phpbbireland/echo/ayla/kle/ansi_2024-11-16.png

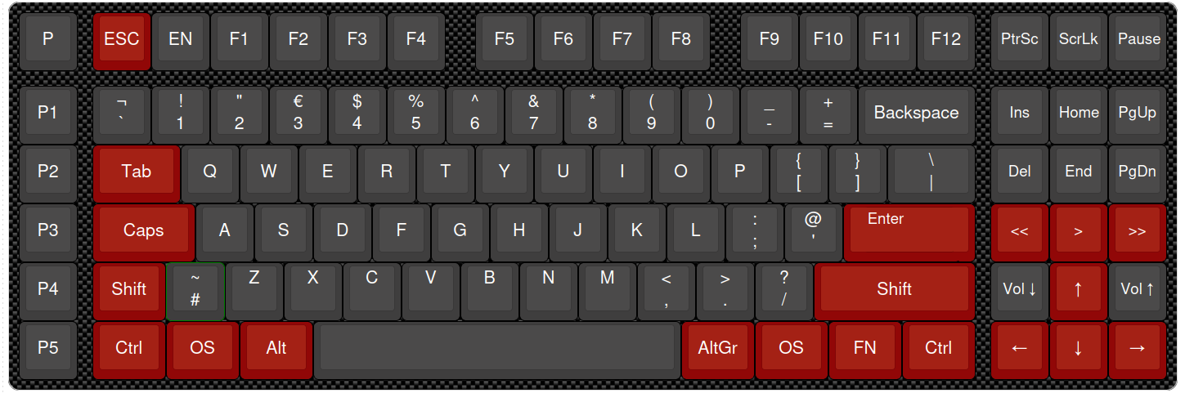
ayla/kle/ansi_2024-11-16.png
