phpbbireland/echo/ayla/kle/ayla80-16-11-24.png

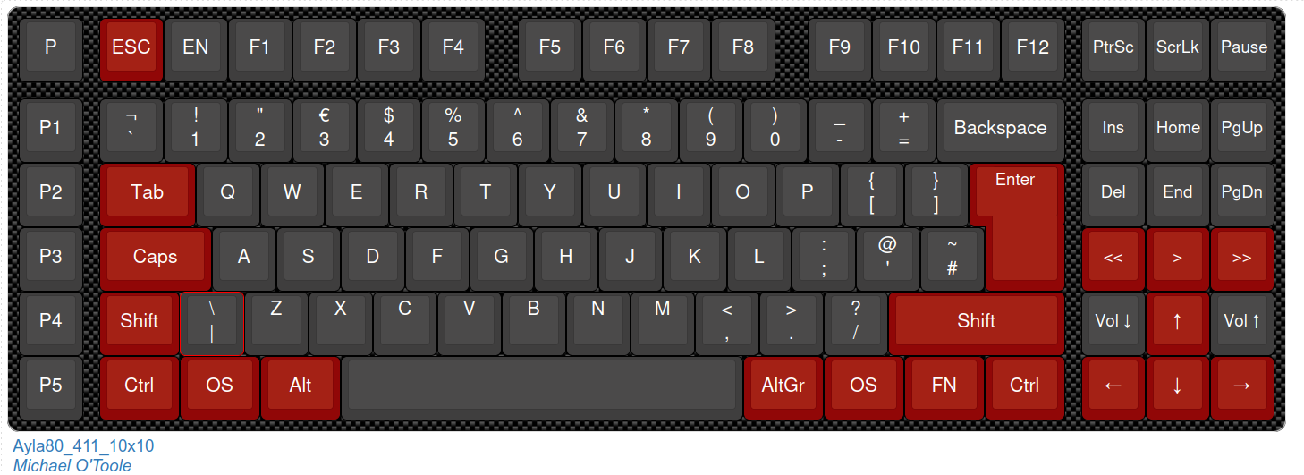
ayla/kle/ayla80-16-11-24.png
