phpbbireland/echo/ayla/kle/kle_ansi.png

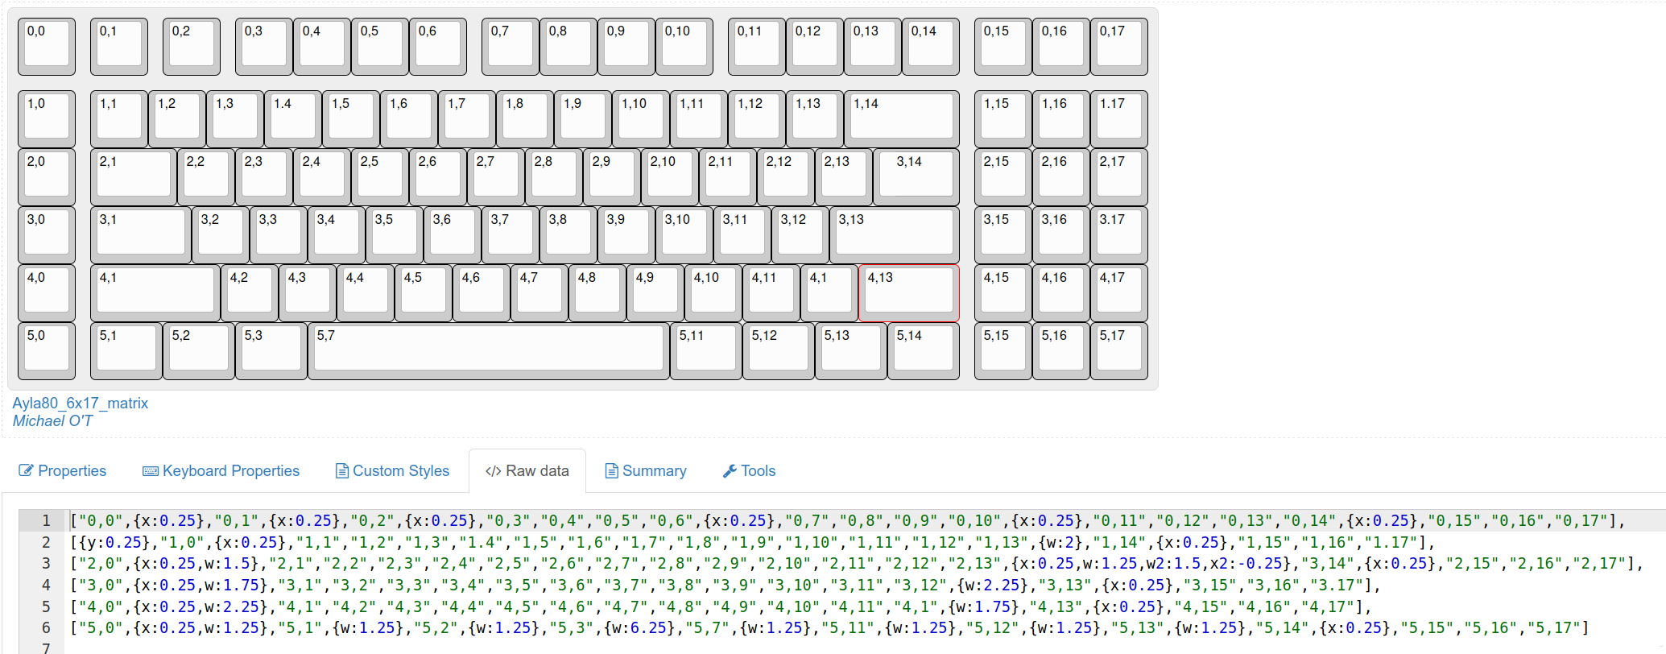
ayla/kle/kle_ansi.png
