phpbbireland/echo/E014/images/kle_en014_keyboard_layout.png

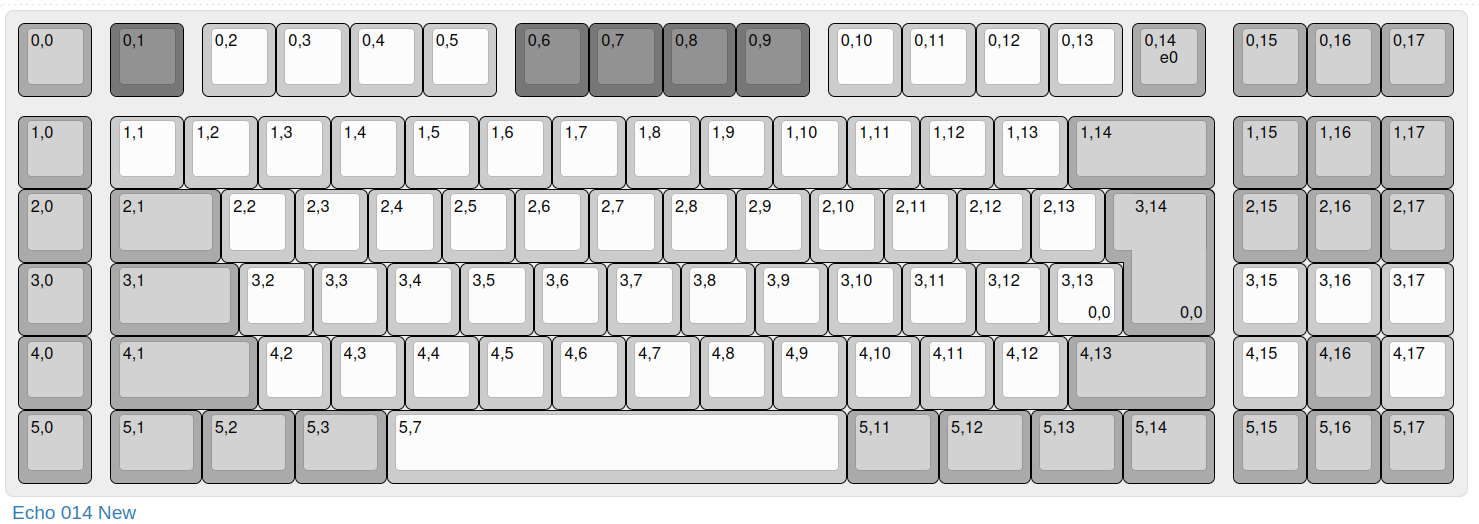
E014/images/kle_en014_keyboard_layout.png
