phpbbireland/echo/iso_encoder/store/kle/kle.png

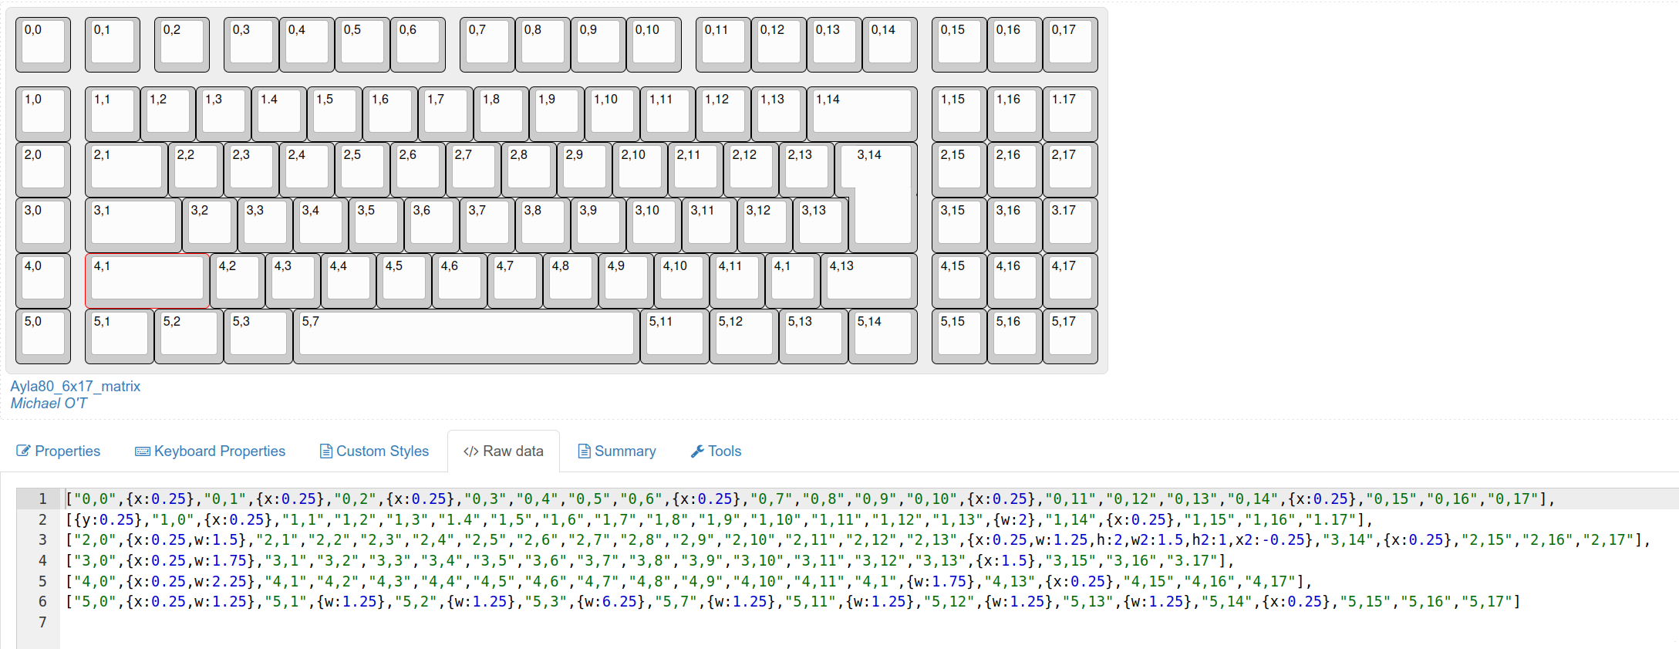
iso_encoder/store/kle/kle.png
