phpbbireland/echo/iso_encoder/store/usevia/usevia-image-ansi.png

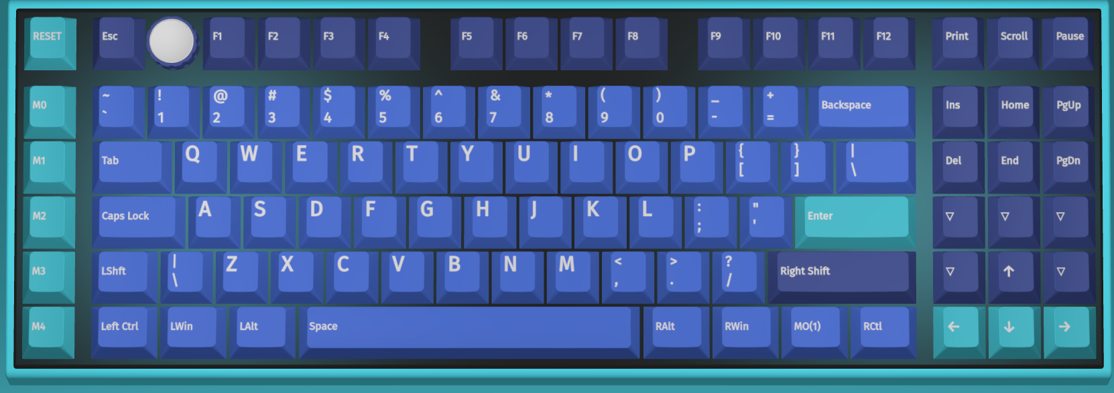
iso_encoder/store/usevia/usevia-image-ansi.png
