phpbbireland/echo/iso_encoder/store/usevia/usevia_image1.png

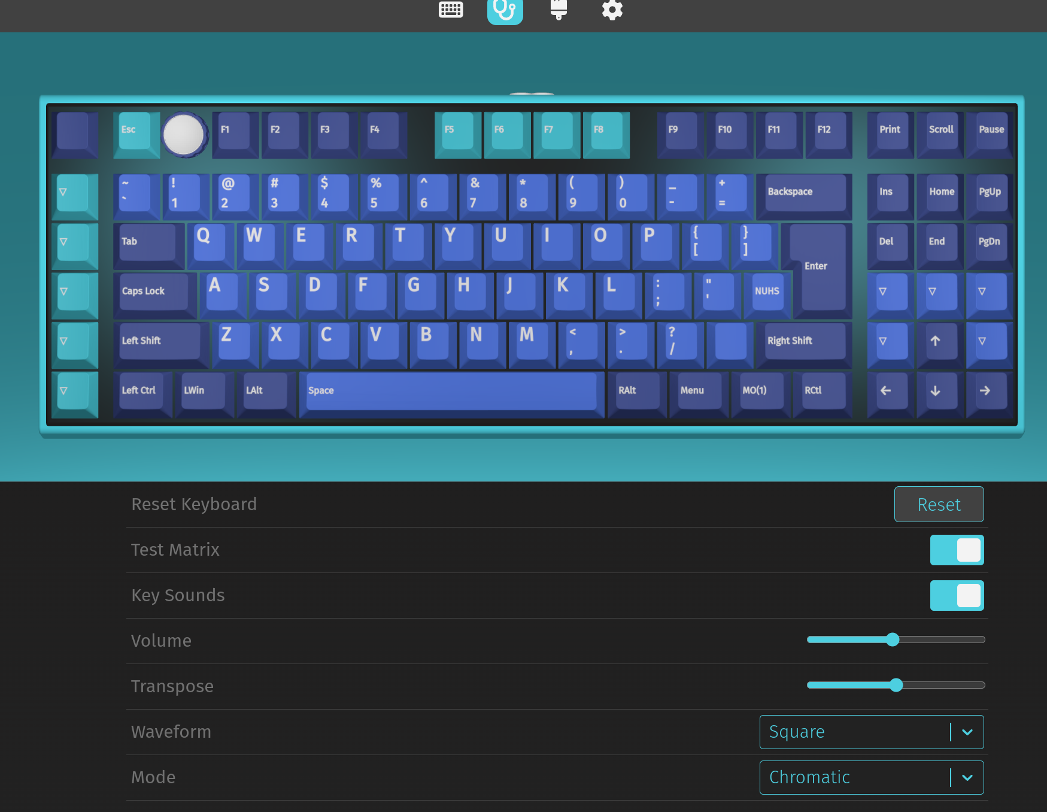
iso_encoder/store/usevia/usevia_image1.png
