phpbbireland/echo/iso_encoder_rp2040_er2/images/kle_image2.png

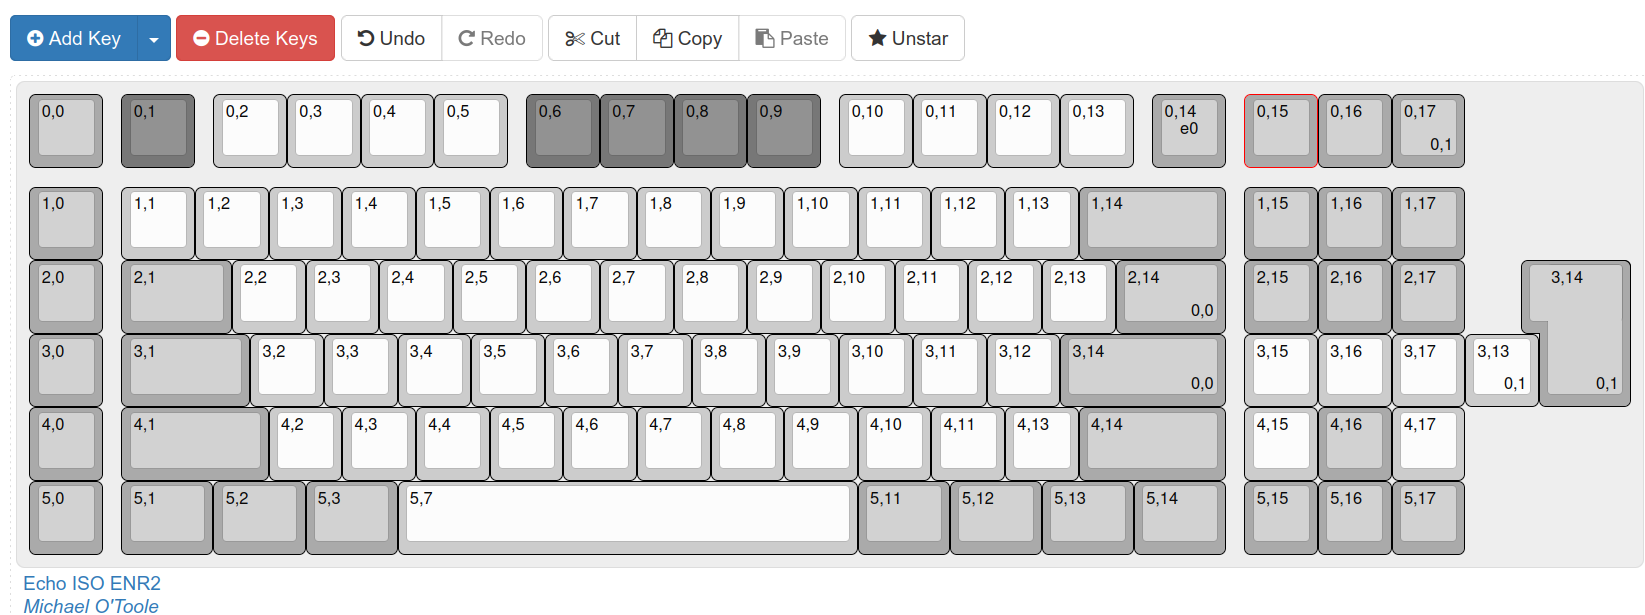
iso_encoder_rp2040_er2/images/kle_image2.png
