phpbbireland/echo/iso_encoder_rp2040_er2/images/usevia.app_image.png

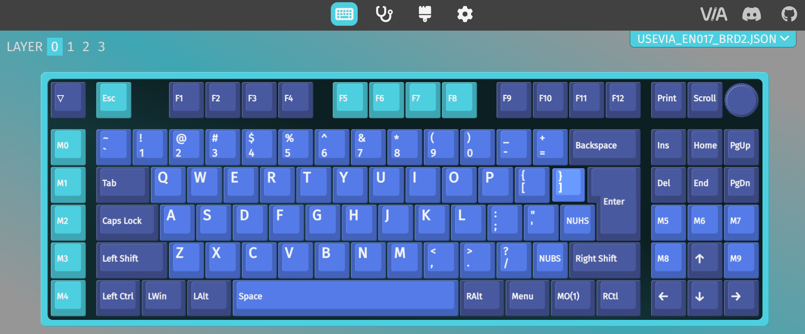
iso_encoder_rp2040_er2/images/usevia.app_image.png
