phpbbireland/echo/Module34C/Module34C.png

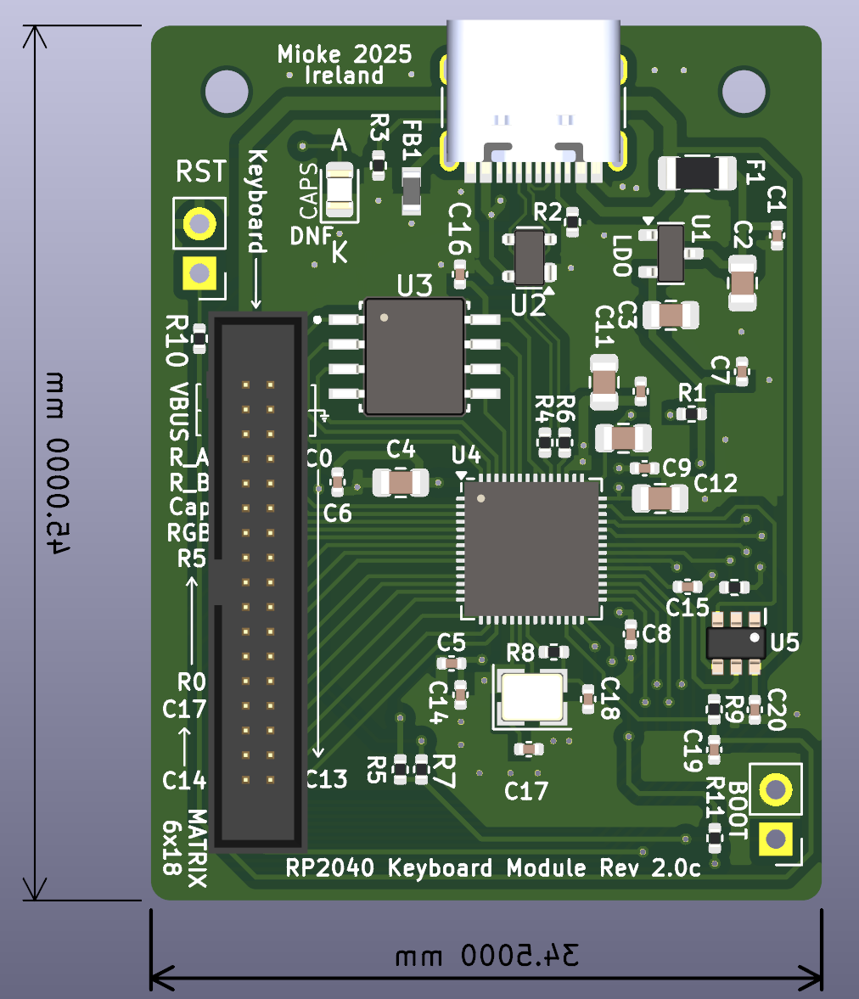
Module34C/Module34C.png
