phpbbireland/echo/RP2024_Module34/images/RP2024_Module_Rev0.1.png

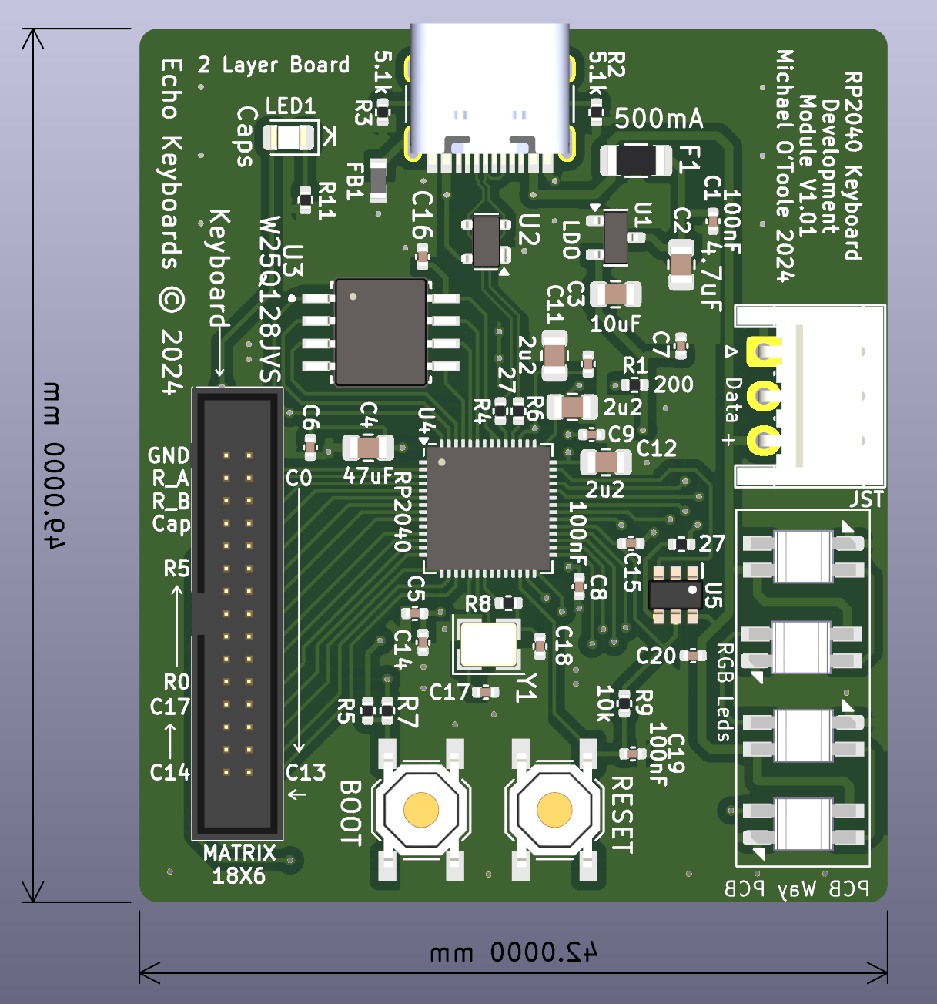
RP2024_Module34/images/RP2024_Module_Rev0.1.png
