phpbbireland/echo/RP2024_Module34/images/RP2024_Module_Rev2.0_34.png

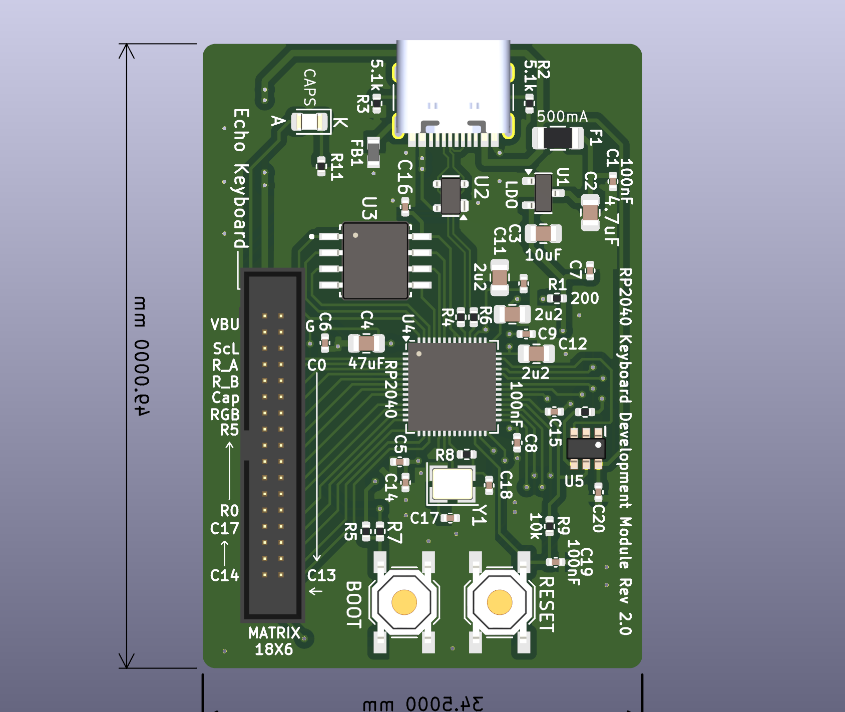
RP2024_Module34/images/RP2024_Module_Rev2.0_34.png
