phpbbireland/echo/RP2024_Module34/images/usevia_image.png

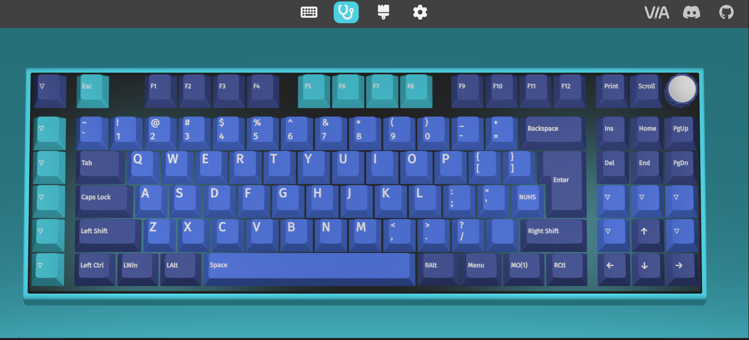
RP2024_Module34/images/usevia_image.png
