phpbbireland/echo/iso_encoder/store/kle/wiring.png

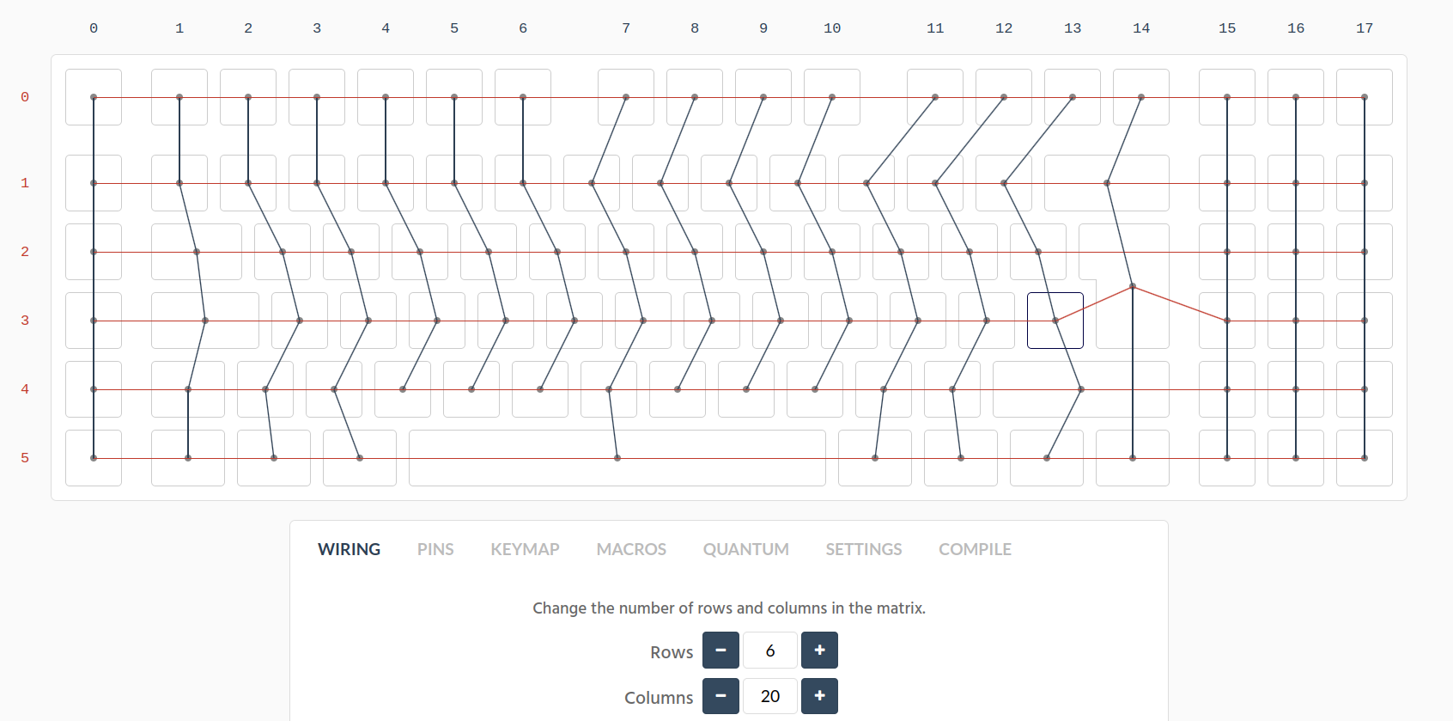
iso_encoder/store/kle/wiring.png
