phpbbireland/echo/iso_encoder/Echo_Ayla_Final/NewMXtest.kicad_sch

## KiCad design iso_encoder/Echo_Ayla_Final/NewMXtest.kicad_sch (2024-11-29)

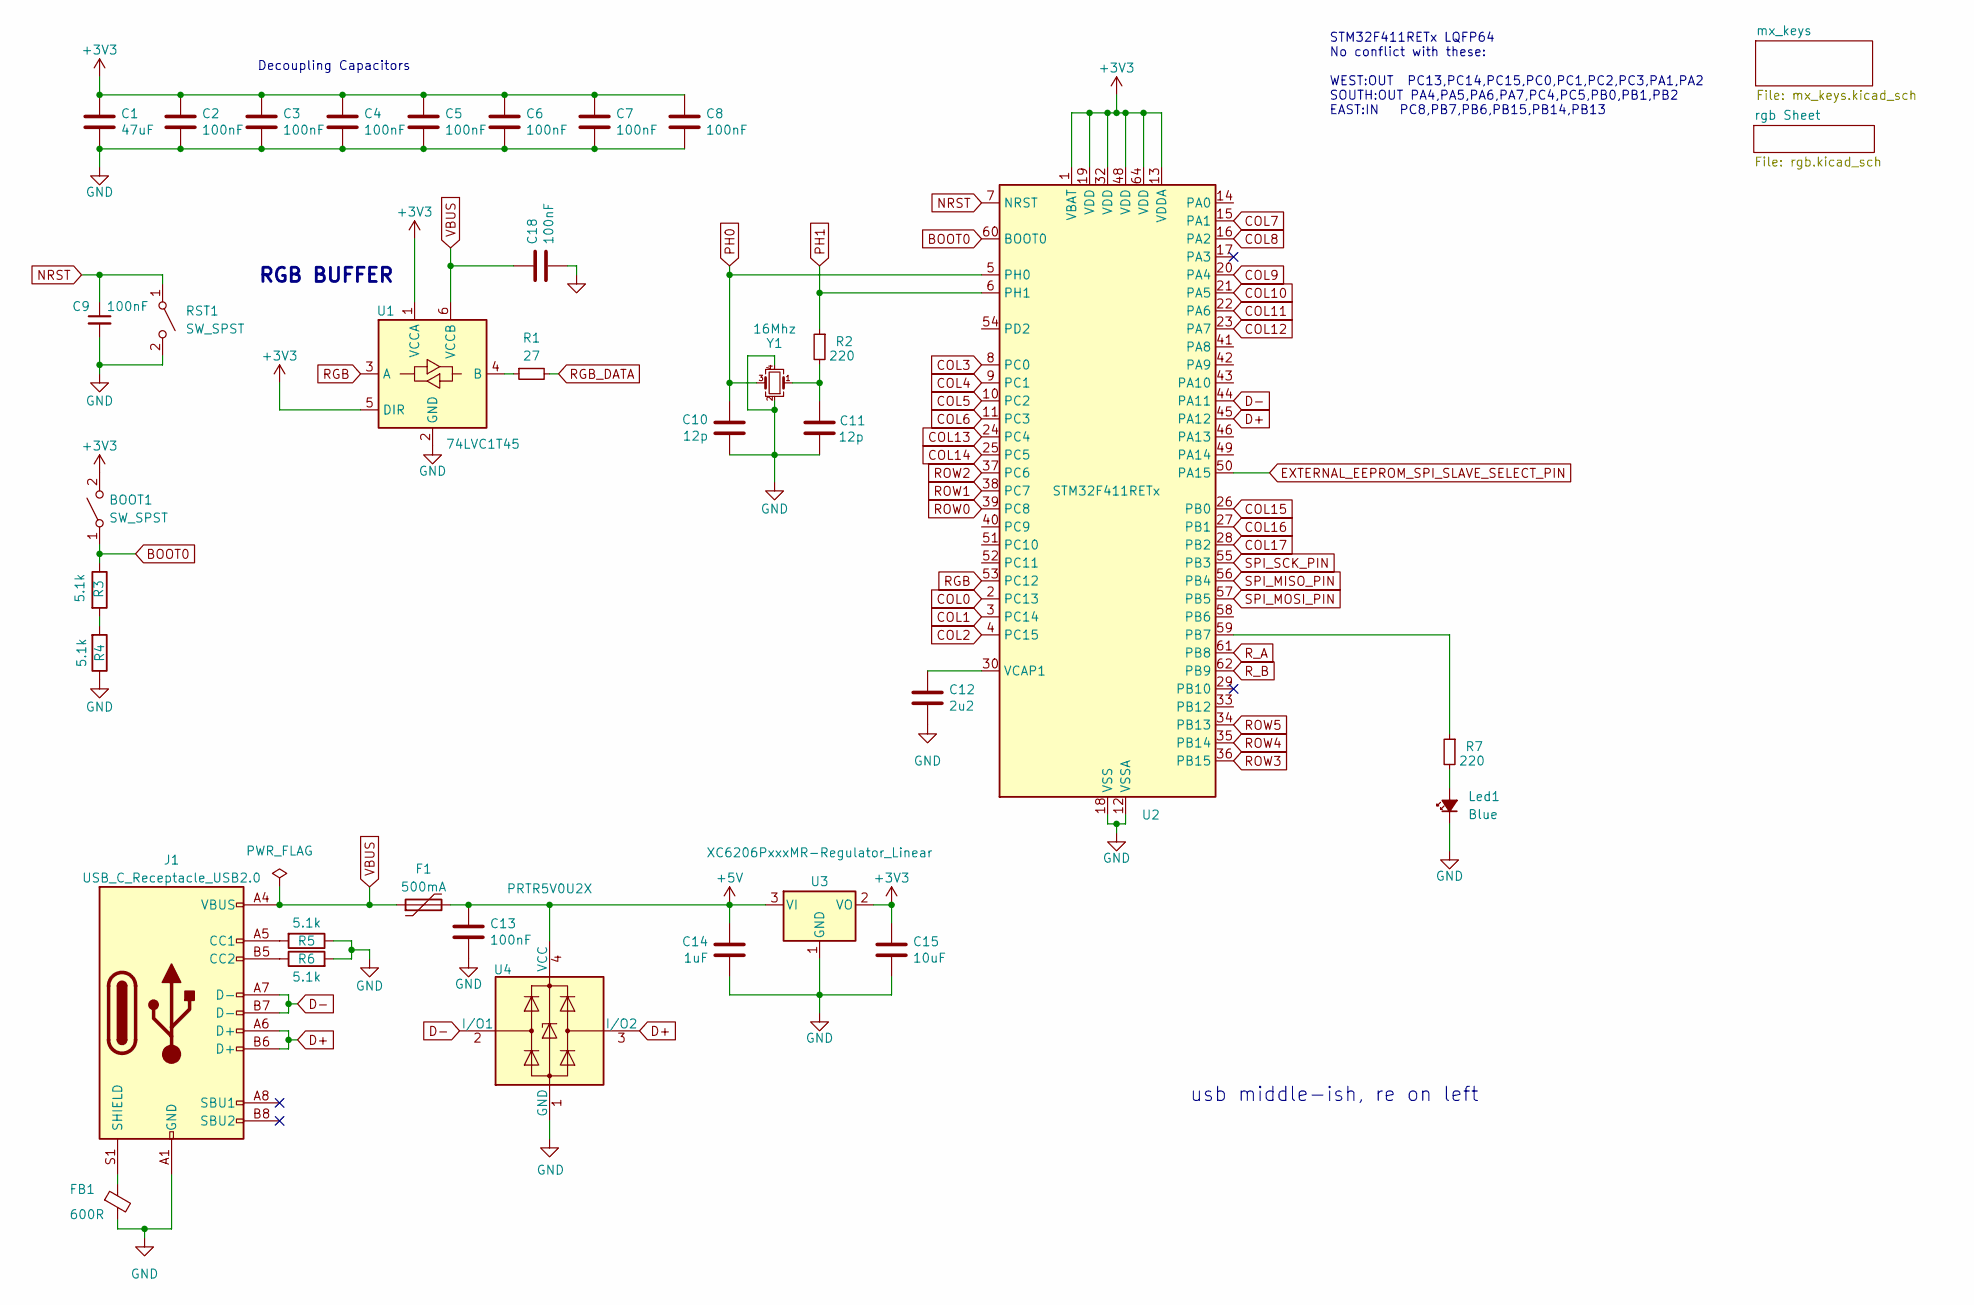
[picture p41: schematic NewMXtest.kicad_sch]

Parts:
BOOT1: SW_SPST; SW_SPST_TL3342
C1: 47uF; C_0805_2012Metric; LCSC C307331
C2, C3, C4, C5, C6, C7, C8, C9, C13, C18: 100nF; C_0402_1005Metric; LCSC C307331
C10, C11: 12p; C_0402_1005Metric; LCSC C307331
C12: 2u2; C_0805_2012Metric; LCSC C307331
C14: 1uF; C_0805_2012Metric; LCSC C307331
C15: 10uF; C_0805_2012Metric; LCSC C307331
F1: 500mA; Fuse_1206_3216Metric; LCSC C135341
FB1: 600R; BEADC1608X95N
J1: USB_C_Receptacle_USB2.0; USB_C_Receptacle_HRO_TYPE-C-31-M-12; JlcRotOffset 180
Led1: Blue; LED_0603_1608Metric
R1: 27; R_0402_1005Metric
R2, R7: 220; R_0402_1005Metric
R3, R4, R5, R6: 5.1k; R_0402_1005Metric
RST1: SW_SPST; SW_SPST_TL3342
U1: 74LVC1T45; SOT-563; MPN 74LVC1T45Z6-7 - SN74LVC1T45DRLR; JLCPCB_CORRECTION 0; 0; 270
U2: STM32F411RETx; LQFP-64_10x10mm_P0.5mm
U3: XC6206PxxxMR-Regulator_Linear; SOT-23; LCSC C5446
U4: PRTR5V0U2X; SOT-143; LCSC C2827688
Y1: 16Mhz; Crystal_SMD_3225-4Pin_3.2x2.5mm

Connections:
+3V3: BOOT1.2 (B), C1.1, C2.1, C3.1, C4.1, C5.1, C6.1, C7.1, C8.1, C15.1, U1.1 (VCCA), U1.5 (DIR), U2.1 (VBAT), U2.13 (VDDA), U2.19 (VDD), U2.32 (VDD), U2.48 (VDD), U2.64 (VDD), U3.2 (VO)
+5V: C13.1, C14.1, F1.2, U3.3 (VI), U4.4 (VCC)
BOOT0: BOOT1.1 (A), R3.1, U2.60 (BOOT0)
COL0: U2.2 (PC13)
COL1: U2.3 (PC14)
COL2: U2.4 (PC15)
COL3: U2.8 (PC0)
COL4: U2.9 (PC1)
COL5: U2.10 (PC2)
COL6: U2.11 (PC3)
COL7: U2.15 (PA1)
COL8: U2.16 (PA2)
COL9: U2.20 (PA4)
COL10: U2.21 (PA5)
COL11: U2.22 (PA6)
COL12: U2.23 (PA7)
COL13: U2.24 (PC4)
COL14: U2.25 (PC5)
COL15: U2.26 (PB0)
COL16: U2.27 (PB1)
COL17: U2.28 (PB2)
D+: J1.A6 (D+), J1.B6 (D+), U2.45 (PA12), U4.3 (I/O2)
D-: J1.A7 (D-), J1.B7 (D-), U2.44 (PA11), U4.2 (I/O1)
EXTERNAL_EEPROM_SPI_SLAVE_SELECT_PIN: U2.50 (PA15)
GND: C1.2, C2.2, C3.2, C4.2, C5.2, C6.2, C7.2, C8.2, C9.2, C10.2, C11.2, C12.2, C13.2, C14.2, C15.2, C18.2, FB1.2, J1.A1 (GND), J1.A12 (GND), J1.B1 (GND), J1.B12 (GND), Led1.1 (K), R4.1, R5.1, R6.2, RST1.2 (B), U1.2 (GND), U2.12 (VSSA), U2.18 (VSS), U2.31 (VSS), U2.47 (VSS), U2.63 (VSS), U3.1 (GND), U4.1 (GND), Y1.2, Y1.4
NRST: C9.1, RST1.1 (A), U2.7 (NRST)
unnamed: C11.1, R2.2, Y1.1
unnamed: C12.1, U2.30 (VCAP1)
unnamed: FB1.1, J1.S1 (SHIELD)
unnamed: J1.A5 (CC1), R5.2
unnamed: J1.B5 (CC2), R6.1
unnamed: Led1.2 (A), R7.2
unnamed: R1.1, U1.4 (B)
unnamed: R3.2, R4.2
unnamed: R7.1, U2.59 (PB7)
PH0: C10.1, U2.5 (PH0), Y1.3
PH1: R2.1, U2.6 (PH1)
RGB: U1.3 (A), U2.53 (PC12)
RGB_DATA: R1.2
ROW0: U2.39 (PC8)
ROW1: U2.38 (PC7)
ROW2: U2.37 (PC6)
ROW3: U2.36 (PB15)
ROW4: U2.35 (PB14)
ROW5: U2.34 (PB13)
R_A: U2.61 (PB8)
R_B: U2.62 (PB9)
SPI_MISO_PIN: U2.56 (PB4)
SPI_MOSI_PIN: U2.57 (PB5)
SPI_SCK_PIN: U2.55 (PB3)
VBUS: C18.1, F1.1, J1.A4 (VBUS), J1.A9 (VBUS), J1.B4 (VBUS), J1.B9 (VBUS), U1.6 (VCCB)

Notes on the sheet:
RGB BUFFER
Decoupling Capacitors
usb middle-ish, re on left
STM32F411RETx LQFP64 No conflict with these: WEST:OUT PC13,PC14,PC15,PC0,PC1,PC2,PC3,PA1,PA2 SOUTH:OUT PA4,PA5,PA6,PA7,PC4,PC5,PB0,PB1,PB2 EAST:IN PC8,PB7,PB6,PB15,PB14,PB13
