phpbbireland/echo/iso_encoder/Echo_Ayla_Final/rgb.kicad_sch

## KiCad design iso_encoder/Echo_Ayla_Final/rgb.kicad_sch (2024-11-29)

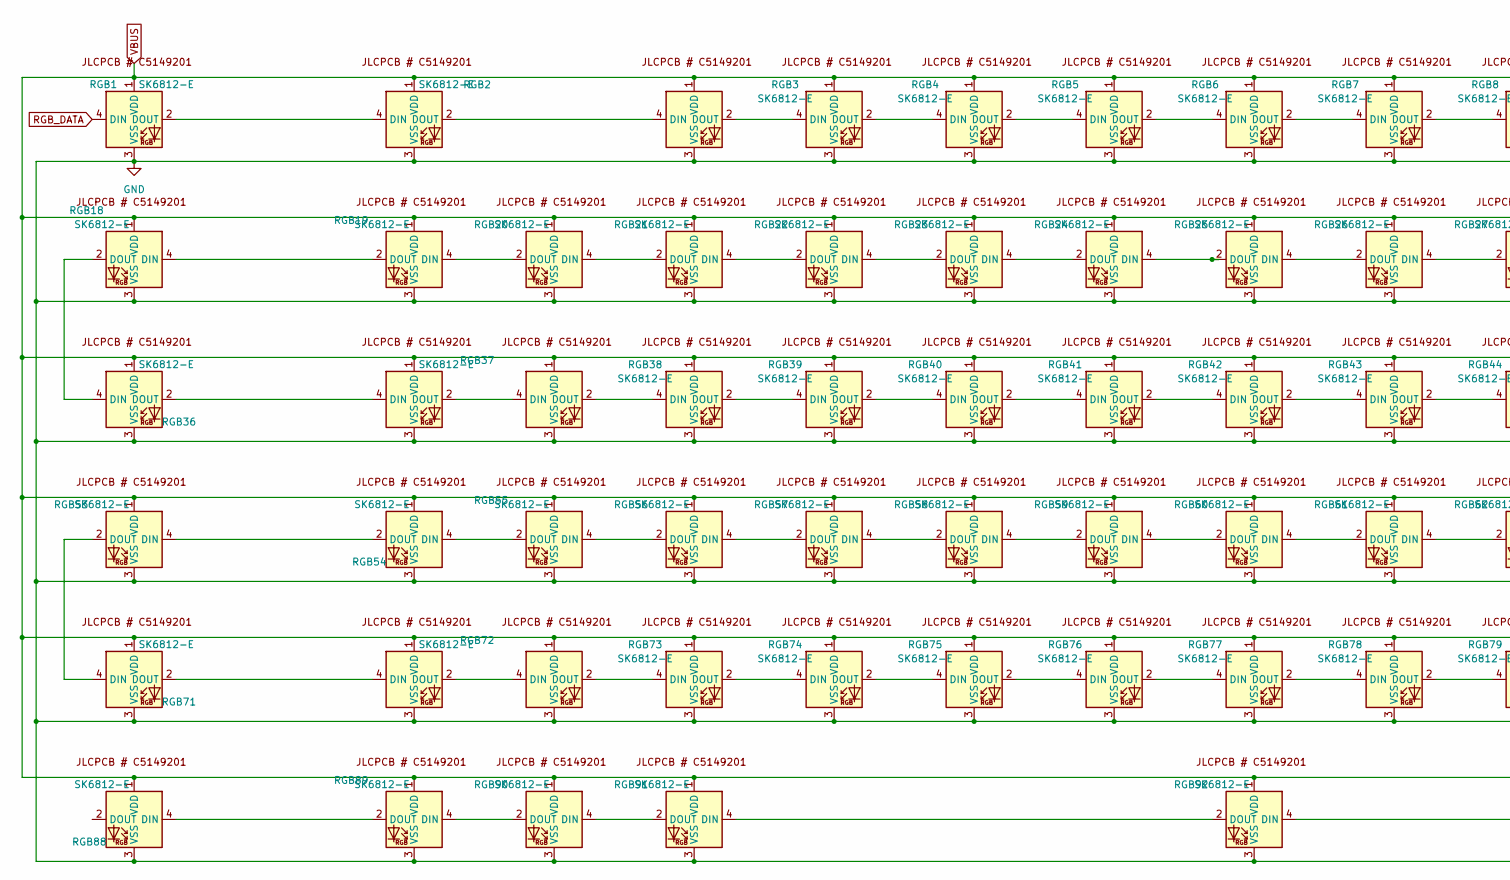
[picture p43: schematic rgb.kicad_sch, part in row 1, column 1]

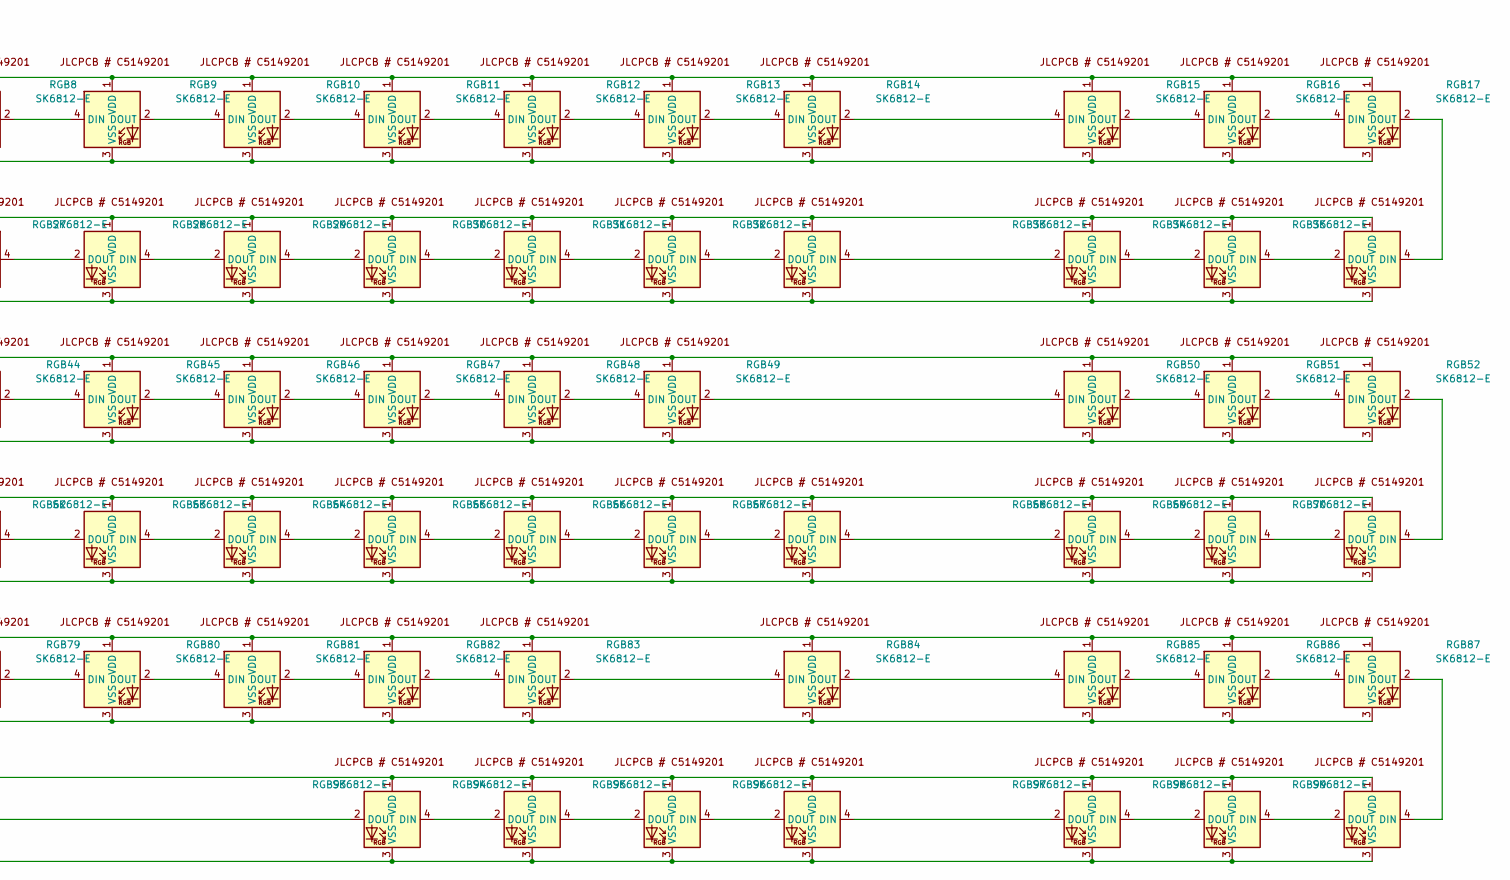
[picture p44: schematic rgb.kicad_sch, part in row 1, column 2]

Parts:
RGB1, RGB2, RGB3, RGB4, RGB5, RGB6, RGB7, RGB8, RGB9, RGB10, RGB11, RGB12, RGB13, RGB14, RGB15, RGB16, RGB17, RGB18, RGB19, RGB20, RGB21, RGB22, RGB23, RGB24, RGB25, RGB26, RGB27, RGB28, RGB29, RGB30, RGB31, RGB32, RGB33, RGB34, RGB35, RGB36, RGB37, RGB38, RGB39, RGB40, RGB41, RGB42, RGB43, RGB44, RGB45, RGB46, RGB47, RGB48, RGB49, RGB50, RGB51, RGB52, RGB53, RGB54, RGB55, RGB56, RGB57, RGB58, RGB59, RGB60, RGB61, RGB62, RGB63, RGB64, RGB65, RGB66, RGB67, RGB68, RGB69, RGB70, RGB71, RGB72, RGB73, RGB74, RGB75, RGB76, RGB77, RGB78, RGB79, RGB80, RGB81, RGB82, RGB83, RGB84, RGB85, RGB86, RGB87, RGB88, RGB89, RGB90, RGB91, RGB92, RGB93, RGB94, RGB95, RGB96, RGB97, RGB98, RGB99: SK6812-E

Connections:
GND: RGB1.3 (VSS), RGB2.3 (VSS), RGB3.3 (VSS), RGB4.3 (VSS), RGB5.3 (VSS), RGB6.3 (VSS), RGB7.3 (VSS), RGB8.3 (VSS), RGB9.3 (VSS), RGB10.3 (VSS), RGB11.3 (VSS), RGB12.3 (VSS), RGB13.3 (VSS), RGB14.3 (VSS), RGB15.3 (VSS), RGB16.3 (VSS), RGB17.3 (VSS), RGB18.3 (VSS), RGB19.3 (VSS), RGB20.3 (VSS), RGB21.3 (VSS), RGB22.3 (VSS), RGB23.3 (VSS), RGB24.3 (VSS), RGB25.3 (VSS), RGB26.3 (VSS), RGB27.3 (VSS), RGB28.3 (VSS), RGB29.3 (VSS), RGB30.3 (VSS), RGB31.3 (VSS), RGB32.3 (VSS), RGB33.3 (VSS), RGB34.3 (VSS), RGB35.3 (VSS), RGB36.3 (VSS), RGB37.3 (VSS), RGB38.3 (VSS), RGB39.3 (VSS), RGB40.3 (VSS), RGB41.3 (VSS), RGB42.3 (VSS), RGB43.3 (VSS), RGB44.3 (VSS), RGB45.3 (VSS), RGB46.3 (VSS), RGB47.3 (VSS), RGB48.3 (VSS), RGB49.3 (VSS), RGB50.3 (VSS), RGB51.3 (VSS), RGB52.3 (VSS), RGB53.3 (VSS), RGB54.3 (VSS), RGB55.3 (VSS), RGB56.3 (VSS), RGB57.3 (VSS), RGB58.3 (VSS), RGB59.3 (VSS), RGB60.3 (VSS), RGB61.3 (VSS), RGB62.3 (VSS), RGB63.3 (VSS), RGB64.3 (VSS), RGB65.3 (VSS), RGB66.3 (VSS), RGB67.3 (VSS), RGB68.3 (VSS), RGB69.3 (VSS), RGB70.3 (VSS), RGB71.3 (VSS), RGB72.3 (VSS), RGB73.3 (VSS), RGB74.3 (VSS), RGB75.3 (VSS), RGB76.3 (VSS), RGB77.3 (VSS), RGB78.3 (VSS), RGB79.3 (VSS), RGB80.3 (VSS), RGB81.3 (VSS), RGB82.3 (VSS), RGB83.3 (VSS), RGB84.3 (VSS), RGB85.3 (VSS), RGB86.3 (VSS), RGB87.3 (VSS), RGB88.3 (VSS), RGB89.3 (VSS), RGB90.3 (VSS), RGB91.3 (VSS), RGB92.3 (VSS), RGB93.3 (VSS), RGB94.3 (VSS), RGB95.3 (VSS), RGB96.3 (VSS), RGB97.3 (VSS), RGB98.3 (VSS), RGB99.3 (VSS)
unnamed: RGB1.2 (DOUT), RGB2.4 (DIN)
unnamed: RGB2.2 (DOUT), RGB3.4 (DIN)
unnamed: RGB3.2 (DOUT), RGB4.4 (DIN)
unnamed: RGB4.2 (DOUT), RGB5.4 (DIN)
unnamed: RGB5.2 (DOUT), RGB6.4 (DIN)
unnamed: RGB6.2 (DOUT), RGB7.4 (DIN)
unnamed: RGB7.2 (DOUT), RGB8.4 (DIN)
unnamed: RGB8.2 (DOUT), RGB9.4 (DIN)
unnamed: RGB10.2 (DOUT), RGB11.4 (DIN)
unnamed: RGB9.2 (DOUT), RGB10.4 (DIN)
unnamed: RGB11.2 (DOUT), RGB12.4 (DIN)
unnamed: RGB12.2 (DOUT), RGB13.4 (DIN)
unnamed: RGB13.2 (DOUT), RGB14.4 (DIN)
unnamed: RGB14.2 (DOUT), RGB15.4 (DIN)
unnamed: RGB15.2 (DOUT), RGB16.4 (DIN)
unnamed: RGB16.2 (DOUT), RGB17.4 (DIN)
unnamed: RGB17.2 (DOUT), RGB35.4 (DIN)
unnamed: RGB18.2 (DOUT), RGB36.4 (DIN)
unnamed: RGB18.4 (DIN), RGB19.2 (DOUT)
unnamed: RGB19.4 (DIN), RGB20.2 (DOUT)
unnamed: RGB20.4 (DIN), RGB21.2 (DOUT)
unnamed: RGB21.4 (DIN), RGB22.2 (DOUT)
unnamed: RGB22.4 (DIN), RGB23.2 (DOUT)
unnamed: RGB23.4 (DIN), RGB24.2 (DOUT)
unnamed: RGB24.4 (DIN), RGB25.2 (DOUT)
unnamed: RGB25.4 (DIN), RGB26.2 (DOUT)
unnamed: RGB26.4 (DIN), RGB27.2 (DOUT)
unnamed: RGB27.4 (DIN), RGB28.2 (DOUT)
unnamed: RGB28.4 (DIN), RGB29.2 (DOUT)
unnamed: RGB29.4 (DIN), RGB30.2 (DOUT)
unnamed: RGB30.4 (DIN), RGB31.2 (DOUT)
unnamed: RGB31.4 (DIN), RGB32.2 (DOUT)
unnamed: RGB32.4 (DIN), RGB33.2 (DOUT)
unnamed: RGB33.4 (DIN), RGB34.2 (DOUT)
unnamed: RGB34.4 (DIN), RGB35.2 (DOUT)
unnamed: RGB36.2 (DOUT), RGB37.4 (DIN)
unnamed: RGB37.2 (DOUT), RGB38.4 (DIN)
unnamed: RGB38.2 (DOUT), RGB39.4 (DIN)
unnamed: RGB39.2 (DOUT), RGB40.4 (DIN)
unnamed: RGB40.2 (DOUT), RGB41.4 (DIN)
unnamed: RGB41.2 (DOUT), RGB42.4 (DIN)
unnamed: RGB42.2 (DOUT), RGB43.4 (DIN)
unnamed: RGB43.2 (DOUT), RGB44.4 (DIN)
unnamed: RGB44.2 (DOUT), RGB45.4 (DIN)
unnamed: RGB45.2 (DOUT), RGB46.4 (DIN)
unnamed: RGB46.2 (DOUT), RGB47.4 (DIN)
unnamed: RGB47.2 (DOUT), RGB48.4 (DIN)
unnamed: RGB48.2 (DOUT), RGB49.4 (DIN)
unnamed: RGB49.2 (DOUT), RGB50.4 (DIN)
unnamed: RGB50.2 (DOUT), RGB51.4 (DIN)
unnamed: RGB51.2 (DOUT), RGB52.4 (DIN)
unnamed: RGB52.2 (DOUT), RGB70.4 (DIN)
unnamed: RGB53.2 (DOUT), RGB71.4 (DIN)
unnamed: RGB53.4 (DIN), RGB54.2 (DOUT)
unnamed: RGB54.4 (DIN), RGB55.2 (DOUT)
unnamed: RGB55.4 (DIN), RGB56.2 (DOUT)
unnamed: RGB56.4 (DIN), RGB57.2 (DOUT)
unnamed: RGB57.4 (DIN), RGB58.2 (DOUT)
unnamed: RGB58.4 (DIN), RGB59.2 (DOUT)
unnamed: RGB59.4 (DIN), RGB60.2 (DOUT)
unnamed: RGB60.4 (DIN), RGB61.2 (DOUT)
unnamed: RGB61.4 (DIN), RGB62.2 (DOUT)
unnamed: RGB62.4 (DIN), RGB63.2 (DOUT)
unnamed: RGB63.4 (DIN), RGB64.2 (DOUT)
unnamed: RGB64.4 (DIN), RGB65.2 (DOUT)
unnamed: RGB65.4 (DIN), RGB66.2 (DOUT)
unnamed: RGB66.4 (DIN), RGB67.2 (DOUT)
unnamed: RGB67.4 (DIN), RGB68.2 (DOUT)
unnamed: RGB68.4 (DIN), RGB69.2 (DOUT)
unnamed: RGB69.4 (DIN), RGB70.2 (DOUT)
unnamed: RGB71.2 (DOUT), RGB72.4 (DIN)
unnamed: RGB72.2 (DOUT), RGB73.4 (DIN)
unnamed: RGB73.2 (DOUT), RGB74.4 (DIN)
unnamed: RGB74.2 (DOUT), RGB75.4 (DIN)
unnamed: RGB75.2 (DOUT), RGB76.4 (DIN)
unnamed: RGB76.2 (DOUT), RGB77.4 (DIN)
unnamed: RGB77.2 (DOUT), RGB78.4 (DIN)
unnamed: RGB78.2 (DOUT), RGB79.4 (DIN)
unnamed: RGB79.2 (DOUT), RGB80.4 (DIN)
unnamed: RGB80.2 (DOUT), RGB81.4 (DIN)
unnamed: RGB81.2 (DOUT), RGB82.4 (DIN)
unnamed: RGB82.2 (DOUT), RGB83.4 (DIN)
unnamed: RGB83.2 (DOUT), RGB84.4 (DIN)
unnamed: RGB84.2 (DOUT), RGB85.4 (DIN)
unnamed: RGB85.2 (DOUT), RGB86.4 (DIN)
unnamed: RGB86.2 (DOUT), RGB87.4 (DIN)
unnamed: RGB87.2 (DOUT), RGB99.4 (DIN)
unnamed: RGB88.4 (DIN), RGB89.2 (DOUT)
unnamed: RGB89.4 (DIN), RGB90.2 (DOUT)
unnamed: RGB90.4 (DIN), RGB91.2 (DOUT)
unnamed: RGB91.4 (DIN), RGB92.2 (DOUT)
unnamed: RGB92.4 (DIN), RGB93.2 (DOUT)
unnamed: RGB93.4 (DIN), RGB94.2 (DOUT)
unnamed: RGB94.4 (DIN), RGB95.2 (DOUT)
unnamed: RGB95.4 (DIN), RGB96.2 (DOUT)
unnamed: RGB96.4 (DIN), RGB97.2 (DOUT)
unnamed: RGB97.4 (DIN), RGB98.2 (DOUT)
unnamed: RGB98.4 (DIN), RGB99.2 (DOUT)
RGB_DATA: RGB1.4 (DIN)
VBUS: RGB1.1 (VDD), RGB2.1 (VDD), RGB3.1 (VDD), RGB4.1 (VDD), RGB5.1 (VDD), RGB6.1 (VDD), RGB7.1 (VDD), RGB8.1 (VDD), RGB9.1 (VDD), RGB10.1 (VDD), RGB11.1 (VDD), RGB12.1 (VDD), RGB13.1 (VDD), RGB14.1 (VDD), RGB15.1 (VDD), RGB16.1 (VDD), RGB17.1 (VDD), RGB18.1 (VDD), RGB19.1 (VDD), RGB20.1 (VDD), RGB21.1 (VDD), RGB22.1 (VDD), RGB23.1 (VDD), RGB24.1 (VDD), RGB25.1 (VDD), RGB26.1 (VDD), RGB27.1 (VDD), RGB28.1 (VDD), RGB29.1 (VDD), RGB30.1 (VDD), RGB31.1 (VDD), RGB32.1 (VDD), RGB33.1 (VDD), RGB34.1 (VDD), RGB35.1 (VDD), RGB36.1 (VDD), RGB37.1 (VDD), RGB38.1 (VDD), RGB39.1 (VDD), RGB40.1 (VDD), RGB41.1 (VDD), RGB42.1 (VDD), RGB43.1 (VDD), RGB44.1 (VDD), RGB45.1 (VDD), RGB46.1 (VDD), RGB47.1 (VDD), RGB48.1 (VDD), RGB49.1 (VDD), RGB50.1 (VDD), RGB51.1 (VDD), RGB52.1 (VDD), RGB53.1 (VDD), RGB54.1 (VDD), RGB55.1 (VDD), RGB56.1 (VDD), RGB57.1 (VDD), RGB58.1 (VDD), RGB59.1 (VDD), RGB60.1 (VDD), RGB61.1 (VDD), RGB62.1 (VDD), RGB63.1 (VDD), RGB64.1 (VDD), RGB65.1 (VDD), RGB66.1 (VDD), RGB67.1 (VDD), RGB68.1 (VDD), RGB69.1 (VDD), RGB70.1 (VDD), RGB71.1 (VDD), RGB72.1 (VDD), RGB73.1 (VDD), RGB74.1 (VDD), RGB75.1 (VDD), RGB76.1 (VDD), RGB77.1 (VDD), RGB78.1 (VDD), RGB79.1 (VDD), RGB80.1 (VDD), RGB81.1 (VDD), RGB82.1 (VDD), RGB83.1 (VDD), RGB84.1 (VDD), RGB85.1 (VDD), RGB86.1 (VDD), RGB87.1 (VDD), RGB88.1 (VDD), RGB89.1 (VDD), RGB90.1 (VDD), RGB91.1 (VDD), RGB92.1 (VDD), RGB93.1 (VDD), RGB94.1 (VDD), RGB95.1 (VDD), RGB96.1 (VDD), RGB97.1 (VDD), RGB98.1 (VDD), RGB99.1 (VDD)
