phpbbireland/echo/E014/qmk/keymaps/via/keymap.c

/* Copyright (C) 2024 Michael O'Toole
 *
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
 * You should have received a copy of the GNU General Public License
 * along with this program.  If not, see <http://www.gnu.org/licenses/>.
 */

// File: echo/iso_encoder/keymaps/via/keymap.c
// Last compiles 26th Dec 2024 ...

#include QMK_KEYBOARD_H


enum layer_names {
    BASE,
    FN,
    FNM,
    FNW
};

/*
           ┌─────────┬─────────┬─────────┬─────────┬─────────┬─────────┬─────────┬─────────┬─────────┬─────────┬─────────┬─────────┬─────────┬─────────┬─────────┬─────────┬─────────┬─────────┐
 RP2040    │  GP0    │   GP1   │   GP2   │   GP3   │   GP4   │   GP5   │   GP6   │   GP7   │   GP8   │   GP9   │   GP10  │   GP11  │   GP12  │   GP13  │   GP14  │   GP16  │   GP17  │   GP18  │
           └─────────┴─────────┴─────────┴─────────┴─────────┴─────────┴─────────┴─────────┴─────────┴─────────┴─────────┴─────────┴─────────┴─────────┴─────────┴─────────┴─────────┴─────────┘
      ┌────┬─────────┬─────────┬─────────┬─────────┬─────────┬─────────┬─────────┬─────────┬─────────┬─────────┬─────────┬─────────┬─────────┬─────────┬─────────┬─────────┬─────────┬─────────┐
      │    │  COL0   │  COL1   │  COL2   │  COL3   │  COL4   │  COL5   │  COL6   │  COL7   │  COL8   │  COL9   │  COL10  │  COL11  │  COL12  │  COL13  │  COL14  │  COL15  │  COL16  │  COL17  │
┌────┐├────┼─────────┼─────────┼─────────┼─────────┼─────────┼─────────┼─────────┼─────────┼─────────┼─────────┼─────────┼─────────┼─────────┼─────────┼─────────┼─────────┼─────────┼─────────┤
│GP19││ROW0│ RESET   │ KC_ESC  │ KC_F1   │ KC_F2   │ KC_F3   │ KC_F4   │ KC_F5   │ KC_F6   │ KC_F7   │ KC_F8   │ KC_F9   │ KC_F10  │ KC_F11  │ KC_F12  │ KC_TRNS │ KC_PSCR │ KC_SCRL │ KC_PAUSE│
├────┤├────┼─────────┼─────────┼─────────┼─────────┼─────────┼─────────┼─────────┼─────────┼─────────┼─────────┼─────────┼─────────┼─────────┼─────────┼─────────┼─────────┼─────────┼─────────┤
│GP20││ROW1│ KC_TRNS │ KC_GRV  │ KC_1    │ KC_2    │ KC_3    │ KC_4    │ KC_5    │ KC_6    │ KC_7    │ KC_8    │ KC_9    │ KC_0    │ KC_MINS │ KC_EQL  │ KC_BSPC │ KC_INS  │ KC_HOME │ KC_PGUP │
├────┤├────┼─────────┼─────────┼─────────┼─────────┼─────────┼─────────┼─────────┼─────────┼─────────┼─────────┼─────────┼─────────┼─────────┼─────────┼─────────┼─────────┼─────────┼─────────┤
│GP21││ROW2│ KC_TRNS │ KC_TAB  │ KC_Q    │ KC_W    │ KC_E    │ KC_R    │ KC_T    │ KC_Y    │ KC_U    │ KC_I    │ KC_O    │ KC_P    │ KC_LBRC │ KC_RBRC │         │ KC_DEL  │ KC_END  │ KC_PGDN │
├────┤├────┼─────────┼─────────┼─────────┼─────────┼─────────┼─────────┼─────────┼─────────┼─────────┼─────────┼─────────┼─────────┼─────────┼─────────┼─────────┼─────────┼─────────┼─────────┤
│GP22││ROW3│ KC_TRNS │ KC_CAPS │ KC_A    │ KC_S    │ KC_D    │ KC_F    │ KC_G    │ KC_H    │ KC_J    │ KC_K    │ KC_L    │ KC_SCLN │ KC_QUOT │ KC_NUHS │ KC_ENTR │ KC_TRNS │ KC_TRNS │ KC_TRNS │
├────┤├────┼─────────┼─────────┼─────────┼─────────┼─────────┼─────────┼─────────┼─────────┼─────────┼─────────┼─────────┼─────────┼─────────┼─────────┼─────────┼─────────┼─────────┼─────────┤
│GP23││ROW4│ KC_TRNS │ KC_LSFT │ KC_Z    │ KC_X    │ KC_C    │ KC_V    │ KC_B    │ KC_N    │ KC_M    │ KC_COMM │ KC_DOT  │ KC_SLSH │ KC_NUBS │ KC_RSFT │         │ KC_TRNS │ KC_UP   │ KC_TRNS │
├────┤├────┼─────────┼─────────┼─────────┼─────────┼─────────┼─────────┼─────────┼─────────┼─────────┼─────────┼─────────┼─────────┼─────────┼─────────┼─────────┼─────────┼─────────┼─────────┤
│GP24││ROW5│ KC_TRNS │ KC_LCTL │ KC_LGUI │ KC_LALT │         │         │         │ KC_SPC  │         │         │         │ KC_RALT │ KC_MENU │ M0(FN)  │ KC_RCTL │ KC_LEFT │ KC_DOWN │ KC_RIGHT│
└────┘└────┴─────────┴─────────┴─────────┴─────────┴─────────┴─────────┴─────────┴─────────┴─────────┴─────────┴─────────┴─────────┴─────────┴─────────┴─────────┴─────────┴─────────┴─────────┘
*/

const uint16_t PROGMEM keymaps[][MATRIX_ROWS][MATRIX_COLS] = {

/*
    Row 0 Col:  0        1        2        3        4        5        6         7        8         9      10       11       12       13                15         16       17
    Row 1 Col:  0        1        2        3        4        5        6         7        8         9      10       11       12       13       14       15         16       17
    Row 2 Col:  0        1        2        3        4        5        6         7        8         9      10       11       12       13                15         16       17
    Row 3 Col:  0        1        2        3        4        5        6         7        8         9      10       11       12       13       14       15         16       17
    Row 4 Col:  0        1        2        3        4        5        6         7        8         9      10       11       12       13                15         16       17
    Row 5 Col:  0        1        2        3                                    7                                  11       12       13       14       15         16       17
*/

    [BASE] = LAYOUT_iso(
                KC_TRNS, KC_ESC,  KC_F1,   KC_F2,   KC_F3,   KC_F4,   KC_F5,   KC_F6,   KC_F7,   KC_F8,   KC_F9,   KC_F10,  KC_F11,  KC_F12,           KC_PSCR,   KC_SCRL, KC_PAUS,
                KC_TRNS, KC_GRV,  KC_1,    KC_2,    KC_3,    KC_4,    KC_5,    KC_6,    KC_7,    KC_8,    KC_9,    KC_0,    KC_MINS, KC_EQL,  KC_BSPC, KC_INSERT, KC_HOME, KC_PGUP,
                KC_TRNS, KC_TAB,  KC_Q,    KC_W,    KC_E,    KC_R,    KC_T,    KC_Y,    KC_U,    KC_I,    KC_O,    KC_P,    KC_LBRC, KC_RBRC,          KC_DEL,    KC_END,  KC_PGDN,
                KC_TRNS, KC_CAPS, KC_A,    KC_S,    KC_D,    KC_F,    KC_G,    KC_H,    KC_J,    KC_K,    KC_L,    KC_SCLN, KC_QUOT, KC_NUHS, KC_ENT,  KC_TRNS,   KC_TRNS, KC_TRNS,
                KC_TRNS, KC_LSFT, KC_Z,    KC_X,    KC_C,    KC_V,    KC_B,    KC_N,    KC_M,    KC_COMM, KC_DOT,  KC_SLSH, KC_NUBS, KC_RSFT,          KC_TRNS,   KC_UP,   KC_TRNS,
                KC_TRNS, KC_LCTL, KC_LGUI, KC_LALT,                            KC_SPC,                             KC_RALT, KC_MENU, MO(FN),  KC_RCTL, KC_LEFT,   KC_DOWN, KC_RIGHT
            ),

    [FN]   = LAYOUT_iso(
                QK_BOOT, _______, _______, _______, _______, _______, _______, _______, _______, _______, _______, _______, _______, _______,          _______,   _______, _______,
                _______, _______, _______, _______, _______, _______, _______, _______, _______, _______, _______, _______, _______, _______, _______, RGB_TOG,   RGB_MOD, RGB_HUI,
                _______, _______, _______, _______, _______, _______, _______, _______, _______, _______, _______, _______, _______, _______,          _______,   _______, _______,
                _______, _______, _______, _______, _______, _______, _______, _______, _______, _______, _______, _______, _______, _______, _______, _______,   _______, _______,
                _______, _______, _______, _______, _______, _______, _______, _______, _______, _______, _______, _______, _______, _______,          _______,   RGB_VAI, _______,
                _______, _______, _______, _______,                            _______,                            _______, _______, _______, _______, RGB_SAD,   RGB_VAD, RGB_SAI
            ),

    [FNM]   = LAYOUT_iso(
                _______, _______, _______, _______, _______, _______, _______, _______, _______, _______, _______, _______, _______, _______,          _______, _______, _______,
                _______, _______, _______, _______, _______, _______, _______, _______, _______, _______, _______, _______, _______, _______, _______, _______, _______, _______,
                _______, _______, _______, _______, _______, _______, _______, _______, _______, _______, _______, _______, _______, _______,          _______, _______, _______,
                _______, _______, _______, _______, _______, _______, _______, _______, _______, _______, _______, _______, _______, _______, _______, _______, _______, _______,
                _______, _______, _______, _______, _______, _______, _______, _______, _______, _______, _______, _______, _______, _______,          _______, _______, _______,
                _______, _______, _______, _______,                            _______,                            _______, _______, _______, _______, _______, _______, _______
            ),
    [FNW]   = LAYOUT_iso(
                _______, _______, _______, _______, _______, _______, _______, _______, _______, _______, _______, _______, _______, _______,          _______, _______, _______,
                _______, _______, _______, _______, _______, _______, _______, _______, _______, _______, _______, _______, _______, _______, _______, _______, _______, _______,
                _______, _______, _______, _______, _______, _______, _______, _______, _______, _______, _______, _______, _______, _______,          _______, _______, _______,
                _______, _______, _______, _______, _______, _______, _______, _______, _______, _______, _______, _______, _______, _______, _______, _______, _______, _______,
                _______, _______, _______, _______, _______, _______, _______, _______, _______, _______, _______, _______, _______, _______,          _______, _______, _______,
                _______, _______, _______, _______,                            _______,                            _______, _______, _______, _______, _______, _______, _______
            ),

};

//ENCODER_MAP_ENABLE is set to yes in rules.mk

#if defined(ENCODER_MAP_ENABLE)
const uint16_t PROGMEM encoder_map[][NUM_ENCODERS][NUM_DIRECTIONS] = {
    [BASE] =   { ENCODER_CCW_CW(KC_VOLD, KC_VOLU) },
    [FN]   =   { ENCODER_CCW_CW(KC_VOLD, KC_VOLU) },
    [FNM]  =   { ENCODER_CCW_CW(UG_HUED, UG_HUEU) },
    [FNW]  =   { ENCODER_CCW_CW(RGB_VAI, RGB_VAD) }
    //
};
#endif
